terriblefire/tf536/rtl/gayle.v

`timescale 1ns / 1ps

/*
TF536 - 68030 Accelerator for Amiga 500/CDTV

Copyright (c) 2016-2025 Stephen J. Leary

This work is licensed under the Creative Commons Attribution-NoDerivatives
4.0 International License. To view a copy of this license, visit
http://creativecommons.org/licenses/by-nd/4.0/ or send a letter to
Creative Commons, PO Box 1866, Mountain View, CA 94042, USA.
*/

module gayle(
           input    CLKCPU,
           input    RESET,
           input    DS20,
           input    AS20,
           input    RW,
           input    IDE_INT,
           output   INT2,
           input [31:0] A,
           input    DIN,
           output   DOUT,
           output   ACCESS
       );

parameter GAYLE_ID_VAL = 4'hd;

// $DE0000 or $DA8000 (Ignores A18)
wire GAYLE_REGS = (A[31:15] != {16'h00DA, 1'b1});
wire GAYLE_ID   = (A[31:15] != {16'h00DE, 1'b0});
wire GAYLE_ACCESS = (GAYLE_ID & GAYLE_REGS);

reg data_out = 1'b0;

reg [3:0] gayleid = GAYLE_ID_VAL;

reg intena = 1'b0;
reg intlast = 1'b0;

// $DE1000
localparam GAYLE_ID_RD = {1'b1,2'h1,1'b1};
localparam GAYLE_ID_WR = {1'b1,2'h1,1'b0};

// $DA8000
localparam GAYLE_STAT_RD = {3'h0,1'b1};
localparam GAYLE_STAT_WR = {3'h0,1'b0};

// $DA9000
localparam GAYLE_INTCHG_RD = {3'h1,1'b1};
localparam GAYLE_INTCHG_WR = {3'h1,1'b0};

// $DAA000
localparam GAYLE_INTENA_RD = {3'h2,1'b1};
localparam GAYLE_INTENA_WR = {3'h2,1'b0};

wire INT_CHNG;
wire INT_CHNG_ACCESS = {(GAYLE_ACCESS | AS20),A[18],{A[13:12]},RW} != {1'b0,GAYLE_INTCHG_WR};

wire DS = DS20 | GAYLE_ACCESS | AS20;

FDCPE #(.INIT(1'b1))
      INT_CHNG_FF (
          .Q(INT_CHNG), // Data output
          .C(~DS), // Clock input
          .CE(~INT_CHNG_ACCESS), // CLOCK ENABLE
          .CLR(~RESET), // Asynchronous clear input
          .D(DIN & INT_CHNG), // Data input
          .PRE(({IDE_INT, intlast} == 2'b10) & intena) // Asynchronous set input
      );


always @(posedge CLKCPU) begin

    intlast <= IDE_INT;

end

always @(negedge DS or negedge RESET) begin

    if (RESET == 1'b0) begin

        // resetting to low ensures that the next cycle
        intena <= 1'b0;
        gayleid <= 4'hD;

    end else begin

        case ({A[18],{A[13:12]},RW})
            GAYLE_STAT_RD: data_out <= IDE_INT;
            GAYLE_INTCHG_RD: data_out <= INT_CHNG;
            GAYLE_ID_RD: begin
                data_out <=  gayleid[3];
                gayleid <= {gayleid[2:0],1'b1};
            end
            GAYLE_ID_WR: gayleid <= 4'hD;
            GAYLE_INTENA_RD: data_out <= intena;
            GAYLE_INTENA_WR: intena <= DIN;
            default: data_out <= 'b0;
        endcase

    end
end

assign INT2 = ~(INT_CHNG & intena);
assign DOUT = data_out;
assign ACCESS = GAYLE_ACCESS;

endmodule
