terriblefire/tf536/testsuite/rtl/FDCP.v

// $Header: /devl/xcs/repo/env/Databases/CAEInterfaces/xec_libs/data/unisims/FDCP.v,v 1.1 2005/05/10 01:20:03 wloo Exp $

/*

FUNCTION        : D-FLIP-FLOP with async clear, async preset

*/

// `celldefine
`timescale  100 ps / 10 ps

module FDCP (Q, C, CLR, D, PRE);

    parameter INIT = 1'b0;

    output Q;
    reg    Q;

    input  C, CLR, D, PRE;

        always @(posedge CLR or posedge PRE or posedge C)
            if (CLR)
                Q <= 0;
            else if (PRE)
                Q <= 1;
            else
                Q <= D;

endmodule
